laeyue/bca182-freertos-multisensor/docs/evidence/wokwi-buzzer-no-pwm.png

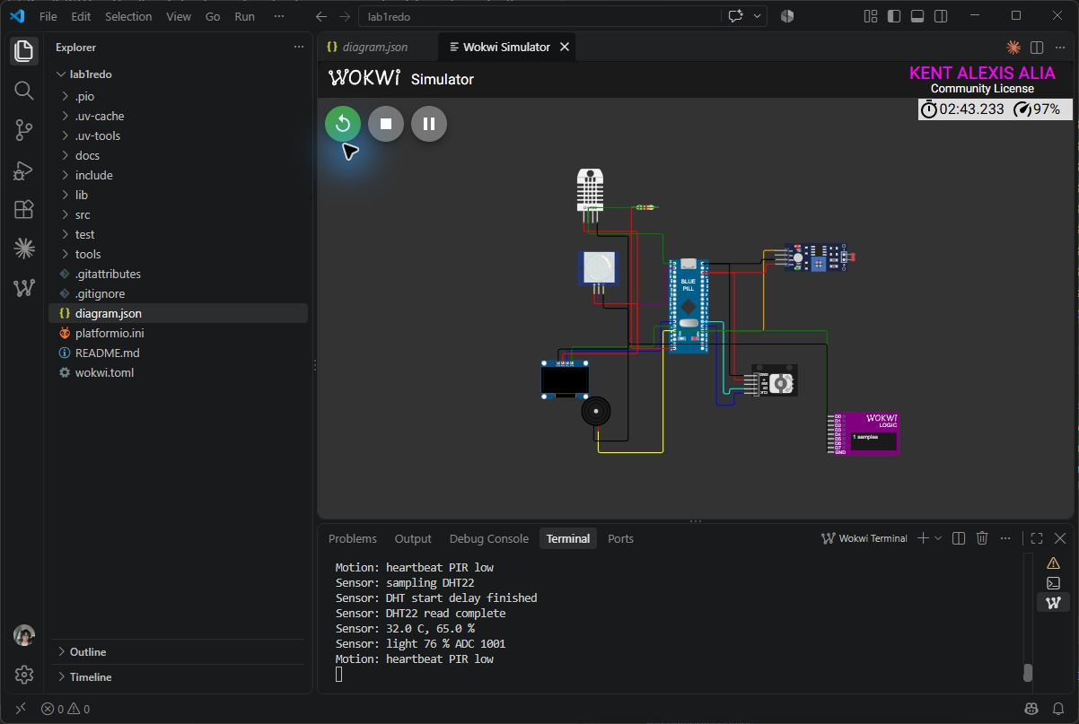
docs/evidence/wokwi-buzzer-no-pwm.png
