laeyue/bca182-freertos-multisensor/docs/evidence/wokwi-production-final.png

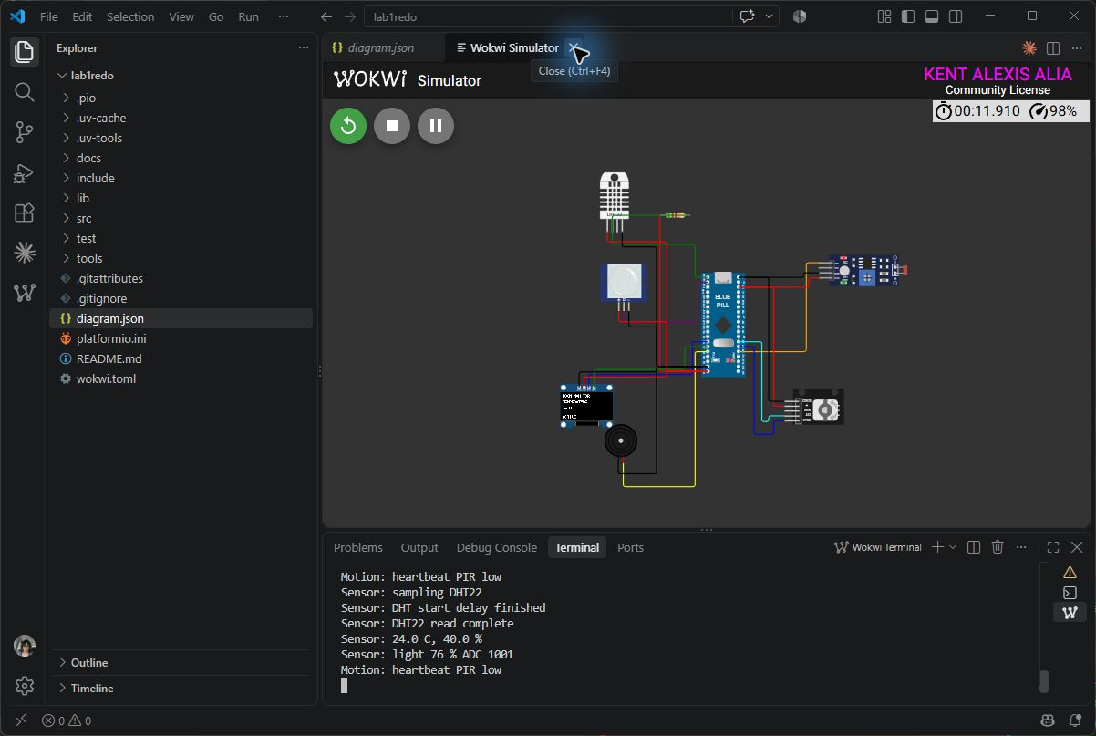
docs/evidence/wokwi-production-final.png
